kkolge/permitme/PCB/PM_I2C_KBRD/KEYBORD_PCB_6_MM_V1/3D/tactile-switch-thru-6mm-series-1.snapshot.25/Tactal Switch -Thru (6mmx 6mmx14.0mm).stp

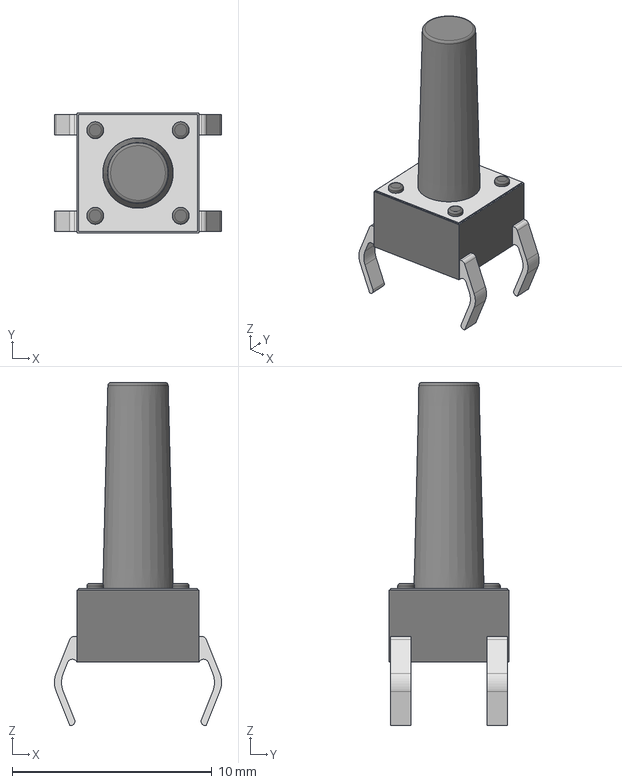
[picture p21: CAD file, 2021-11-13, an earlier design]
PCB/PM_I2C_KBRD/KEYBORD_PCB_6_MM_V1/3D/tactile-switch-thru-6mm-series-1.snapshot.25/Tactal Switch -Thru (6mmx 6mmx14.0mm).stp
8.37 x 5.99 x 17.2 mm
